filipkorus/IoT-weather-station/firmware/firmware_gateway_wifi/include/GlobalVar.h

#ifndef GLOBALVAR_H
#define GLOBALVAR_H

#define BACKEND_IP "iot.fkor.us"
#define WSS true

#ifndef PROD
#define AUTH_TOKEN "AAzsNHPQE2QhnmRdWolQ2wXDtJG91qzIfzQW29iSRnEO846j1MFfOV4zifiZXBgbd4zwGZ17W2RoTD1LqDl6avrkk1CAyzv94eBH8IbtrL5fuM8QcHBAMhOpIad9Af3o"
#define UID "G202411131A"
#endif

// #define UID "G202411131A"

#endif
